AnttiNykanen/asymmetria/firmware/include/user_cgi.h

/**
 * @file user_cgi.h
 * @brief Application-specific CGI handler definitions
 *
 * @author Antti Nykänen <aon@umetronics.com>
 */

#pragma once

#include "httpd.h"

int user_cgi_set_status(HttpdConnData *conn_data);
int user_cgi_set_dimmer(HttpdConnData *conn_data);
int user_cgi_get_dimmer(HttpdConnData *conn_data);
